FugLong/Azimuth/src/track_network_internal.h

#pragma once

#ifndef IMU_DEBUG_MODE
#define IMU_DEBUG_MODE 1
#endif

#if !IMU_DEBUG_MODE

#include <Arduino.h>
#include <ArduinoJson.h>
#include <DNSServer.h>
#include <Preferences.h>
#include <WebServer.h>
#include <WiFiUdp.h>

#include "opentrack_pose.h"

#ifndef OPENTRACK_UDP_PORT
#define OPENTRACK_UDP_PORT 4242
#endif

#ifndef AZIMUTH_FW_VERSION
#define AZIMUTH_FW_VERSION "dev"
#endif

#ifndef AZIMUTH_RELEASE_MANIFEST_URL
#define AZIMUTH_RELEASE_MANIFEST_URL "https://fuglong.github.io/Azimuth/manifest.json"
#endif

#ifndef AZIMUTH_RELEASE_FLASHER_URL
#define AZIMUTH_RELEASE_FLASHER_URL "https://fuglong.github.io/Azimuth/"
#endif

#ifndef AZIMUTH_RELEASE_MANIFEST_CA_CERT
#define AZIMUTH_RELEASE_MANIFEST_CA_CERT ""
#endif

namespace azimuth_net {

constexpr uint16_t kWebPortSta = 8080;
constexpr uint16_t kWebPortAp = 80;
constexpr const char* kPrefsNs = "azimuth";
constexpr const char* kPrefsKeyBatteryCapacityMah = "bat_cap";
constexpr const char* kPrefsKeyBatteryCalOffsetMv = "bat_cal";
constexpr const char* kPrefsKeyLedR = "led_r";
constexpr const char* kPrefsKeyLedG = "led_g";
constexpr const char* kPrefsKeyLedB = "led_b";
constexpr uint32_t kWifiConnectTimeoutMs = 12000;
constexpr const char* kOfflineApSsid = "Azimuth-Tracker";

struct NetworkRuntime {
  WebServer webSta;
  WebServer webAp;
  DNSServer dnsCaptive;
  WiFiUDP udp;
  IPAddress otIp;
  String otHostTrimmed;
  bool otHostIsLiteralIp = false;
  uint32_t lastOtDnsMs = 0;
  uint16_t otPort = OPENTRACK_UDP_PORT;
  bool udpSocketOk = false;
  bool udpSendEnabled = true;
  bool staWebActive = false;
  bool apPortalActive = false;
  bool offlineApMode = false;
  bool fwUpdateCheckDone = false;
  bool fwUpdateAvailable = false;
  String fwLatestVersion;
  uint8_t fwUpdateCheckAttempts = 0;
  uint32_t fwUpdateNextCheckMs = 0;
  String fwUpdateLastError;
  Preferences prefs;
  bool prefsOpened = false;
  uint16_t imuPeriodMsRuntime = 10;
  bool imuDynamicRuntime = true;
  bool hatireUsbRuntime = true;
  /** Set when portal saves IMU interval / dynamic prefs without reboot — main applies BNO08x period. */
  bool imuReportPrefsDirty = false;
  /** Last variable-rate telemetry (rotation-vector period + controller state). */
  uint16_t imuDynTelemAppliedMs = 0;
  uint16_t imuDynTelemWantMs = 0;
  float imuDynTelemActivityDegPerSec = 0.0f;
  float imuDynTelemRawOmegaDegPerSec = 0.0f;
  float imuDynTelemSmoothedPeriodMs = 0.0f;
  uint32_t imuDynTelemLastUpdateMs = 0;
  OtAxisMapConfig otAxisMapRuntime{};
  uint32_t lastPortalActivityMs = 0;
  uint32_t lastUdpTxMs = 0;
  uint32_t lastNetworkServiceMs = 0;
  uint32_t lastBackgroundTickMs = 0;
  bool wifiSleepEnabled = false;
  bool thermalHoldActive = false;
  bool stasisActive = false;
  bool poseValid = false;
  float poseYawDeg = 0.0f;
  float posePitchDeg = 0.0f;
  float poseRollDeg = 0.0f;
  uint32_t poseLastMs = 0;

  NetworkRuntime();
};

extern NetworkRuntime gRuntime;

bool ensurePrefsOpen();
wifi_power_t wifiTxFromProfile(uint8_t profile);
uint8_t mergedWifiTxProfile();
uint16_t mergedImuPeriodMs();
bool mergedImuDynamic();
bool mergedHatireUsb();
bool mergedMdnsOn();
String mergedHostname();
void refreshRuntimeFromPrefs();
void markImuReportPrefsDirty();
bool takeImuReportPrefsDirty();
void publishImuDynamicTelemetry(uint16_t appliedReportMs, uint16_t controllerWantMs,
                                float activityDegPerSec, float rawOmegaDegPerSec, float smoothedPeriodMs);
void applyStaWifiTxPower();
void markPortalActivity();
void applyAdaptiveWifiSleep();
bool hostnameCharsValid(const char* s);
String mergedSsid();
String mergedPass();
String mergedOtHost();
uint16_t mergedOtPort();
bool mergedUdpOn();
uint8_t mergedRgbBrightness();
uint8_t mergedLedMode();
uint8_t mergedLedR();
uint8_t mergedLedG();
uint8_t mergedLedB();
uint8_t mergedBuzzerVolume();
uint16_t mergedBatteryCapacityMah();
int32_t mergedBatteryCalOffsetMv();
void applyIoLevelsFromPrefs();
OtAxisMapConfig mergedOtAxisMap();
void appendOtAxesToJson(JsonDocument& doc);

void maybeRefreshOtHostname();
void applyOtTarget();
void tryOpenUdpSocket();
bool otTargetOk();
void sendOpentrackUdp(float yawDeg, float pitchDeg, float rollDeg);

String portalHttpUrl();
void sendJson(WebServer& http, int code, const JsonDocument& doc);
void registerRoutes(WebServer& http, bool captiveProbeRedirect);
void performFirmwareUpdateCheckOnce();
/**
 * Trust anchor used for the GitHub Pages manifest + OTA download (Let's Encrypt
 * ISRG Root X1, plus an optional compile-time override via
 * `-DAZIMUTH_RELEASE_MANIFEST_CA_CERT=...`). Returned pointer lives for the
 * program lifetime.
 */
const char* releaseRootCaCert();

void applyThermalEmergency();
void startOfflineApPortal();
void networkInit();
void networkLoop();
void loadTrackingPrefs();
uint16_t imuPeriodMsValue();
bool hatireUsbValue();
const OtAxisMapConfig& otAxisMapValue();
void setStasis(bool active);

}  // namespace azimuth_net

#endif  // !IMU_DEBUG_MODE
