FugLong/Azimuth/src/io_buzzer.h

#pragma once

#include <stdint.h>

namespace azimuth_io_buzzer {

void init();
void chirp(uint16_t frequencyHz, uint16_t durationMs);
/** Short non-blocking melody for FUNC button (no-op if buzzer not present). */
void playFuncButtonTune();
/** Distinct “thermal warning” motif (~80 °C edge). */
void playThermalWarnTune();
/** Distinct “thermal emergency” motif (~90 °C); system may cut Wi‑Fi after this. */
void playThermalCriticalTune();
/** Low battery warning motif (non-panic). */
void playBatteryLowTune();
/** Battery critical motif (strong alarm). */
void playBatteryCriticalTune();
/** Short harsh pulse used for 5%..1% battery alerts. */
void playBatteryPanicPulse();
/** Pause/stasis (FUNC) — entering low-power tracking hold. */
void playStasisEnterTune();
/** Resume from stasis. */
void playStasisExitTune();
/** Wireless update started (long-press FUNC or portal trigger). */
void playUpdateStartTune();
/** Wireless update finished successfully (just before reboot into new image). */
void playUpdateOkTune();
/** Wireless update failed; device stays on current image. */
void playUpdateFailTune();
void tick();

/** 0 = mute; 1–100 is UI level (firmware applies a curve to PWM duty). */
void setVolumePercent(uint8_t percent);
/** True while a tone/melody is actively playing. */
bool isActive();

}  // namespace azimuth_io_buzzer
